TTF-fog/hackpad/images/image-2.png

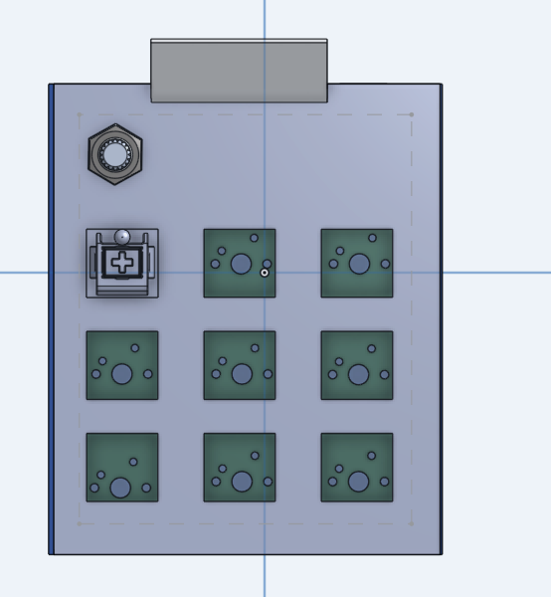
images/image-2.png
